FriedCircuits/FC-USB-Tester-OLED-Backpack/USB_Tester_v2/usb_tester_OLED_128x64_sch.png

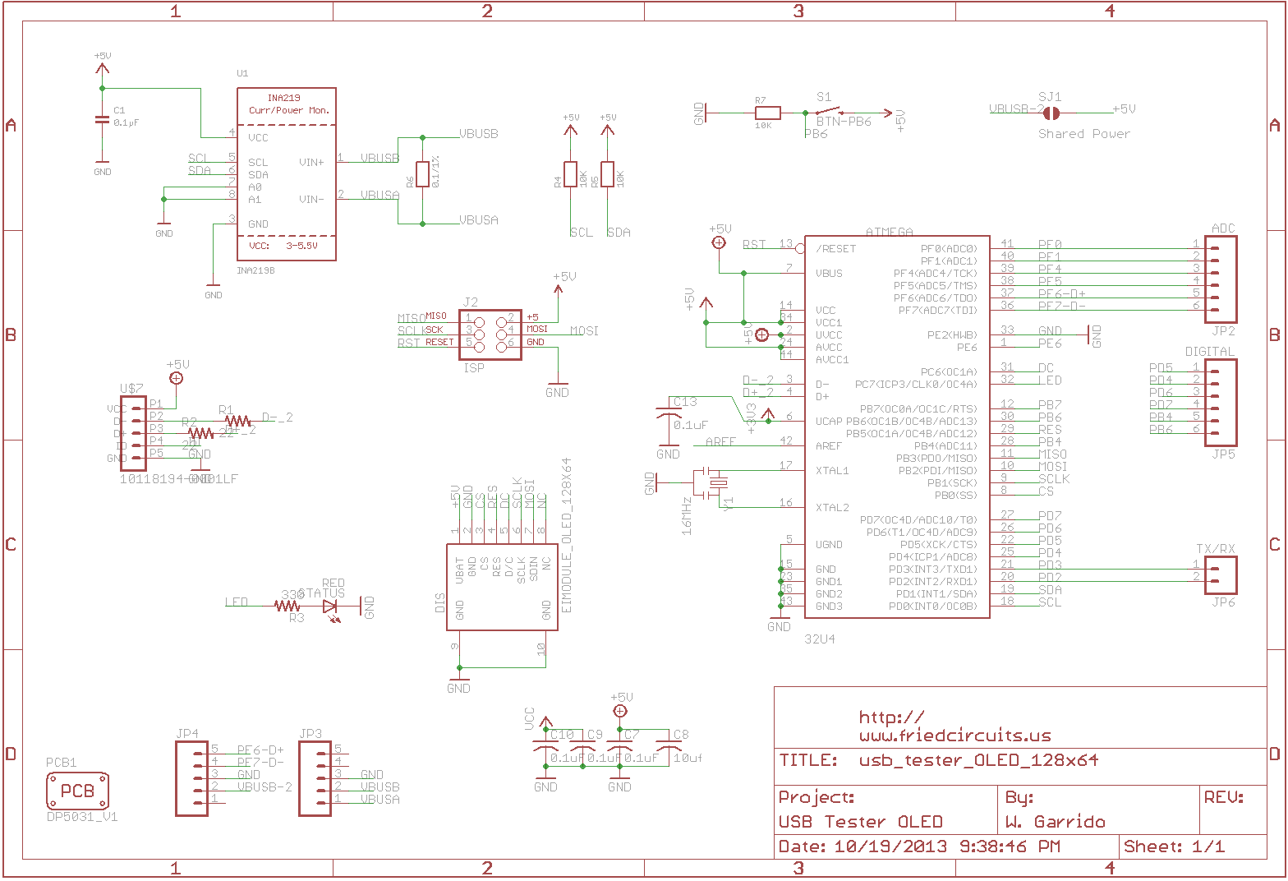
USB_Tester_v2/usb_tester_OLED_128x64_sch.png
